Trasselfrisyr/MIB/MIB-board-mkI/MIBmkI-3.png

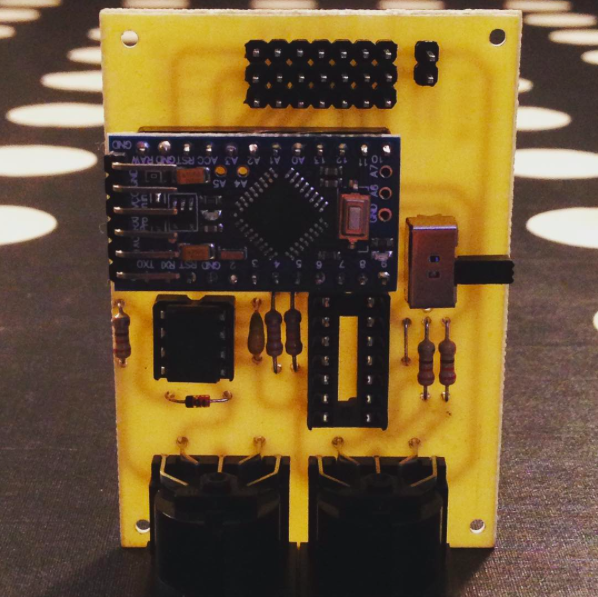
MIB-board-mkI/MIBmkI-3.png
